KeiranCantilina/IOT-Long-Distance-Relationship-Colorcube/Colorcube_ESP8266_V1/interrupt_test/interrupt_test.ino

const int interruptPin = 0; //GPIO 0 (Flash Button) 
const int LED=2; //On board blue LED 
 
void setup() { 
  Serial.begin(115200); 
  pinMode(LED,OUTPUT); 
  pinMode(interruptPin, INPUT_PULLUP); 
  attachInterrupt(digitalPinToInterrupt(interruptPin), handleInterrupt, CHANGE); 
} 
 
void loop() 
{ 
    digitalWrite(LED,HIGH); //LED off 
    delay(1000); 
    digitalWrite(LED,LOW); //LED on 
    delay(1000); 
} 
 
//This program get executed when interrupt is occures i.e.change of input state
ICACHE_RAM_ATTR void handleInterrupt() { 
    Serial.println("Interrupt Detected"); 
}
